dobrinz123/CEAS_TSC/Images/Baterie.png

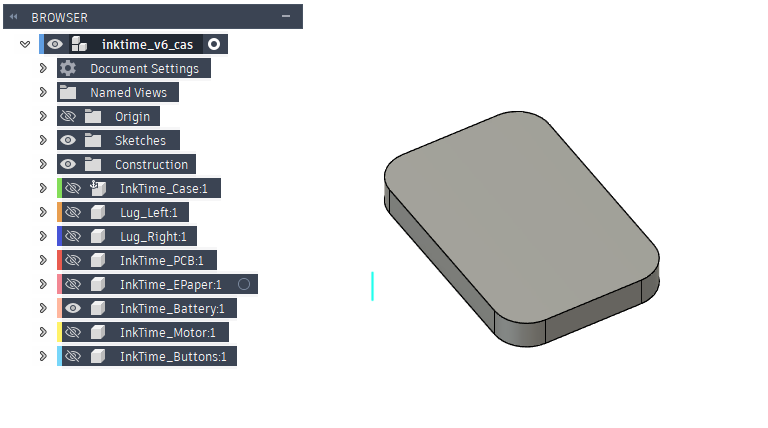
Images/Baterie.png
